james481/cat-trainer/docs/img/base_pcb.png

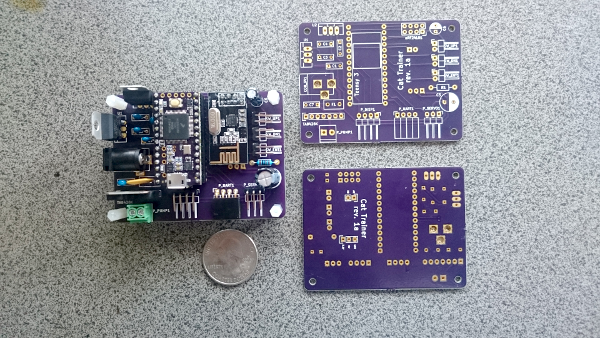
docs/img/base_pcb.png
