james481/cat-trainer/docs/img/base_proto.png

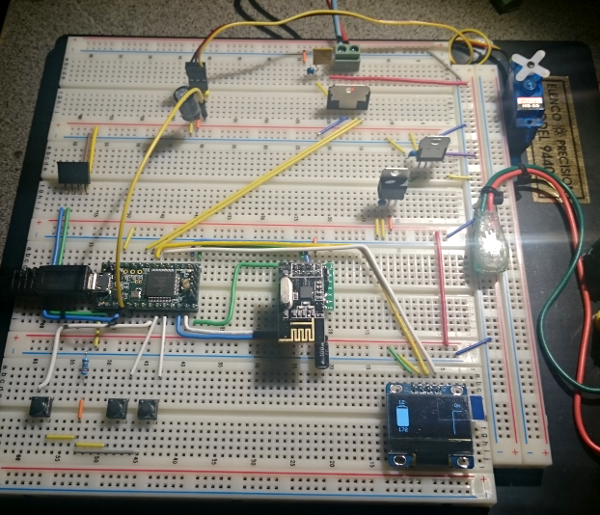
docs/img/base_proto.png
