james481/cat-trainer/docs/img/sensor_hand.png

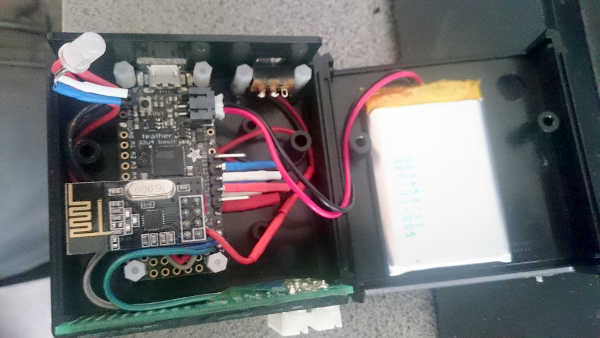
docs/img/sensor_hand.png
