james481/cat-trainer/docs/img/sensor_proto.png

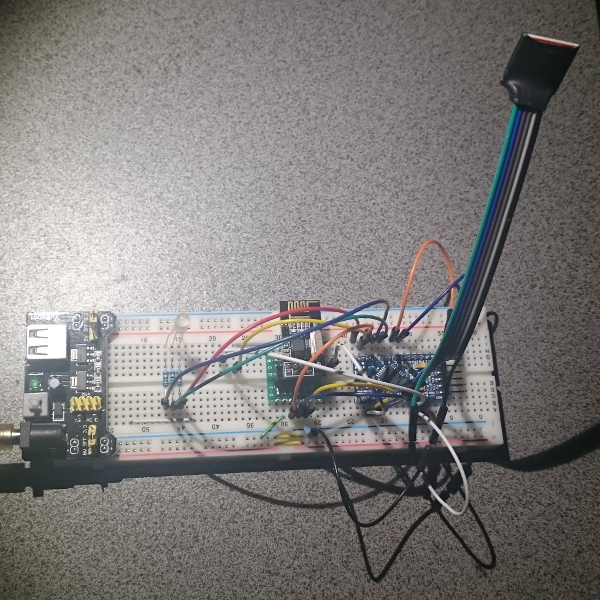
docs/img/sensor_proto.png
