james481/cat-trainer/docs/img/base_setup.png

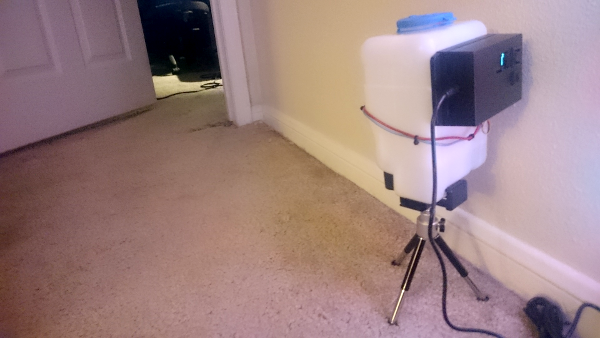
docs/img/base_setup.png
